Savvi-x/wro-Motaqadima/v-photos/WhatsApp Image 2026-09-22 at 7.46.37 PM (2).jpeg

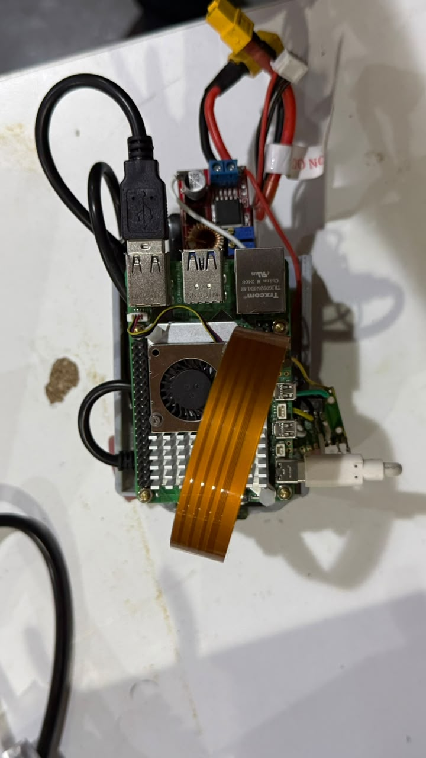
v-photos/WhatsApp Image 2026-09-22 at 7.46.37 PM (2).jpeg
