Savvi-x/wro-Motaqadima/v-photos/WhatsApp Image 2026-09-22 at 7.46.36 PM.jpeg

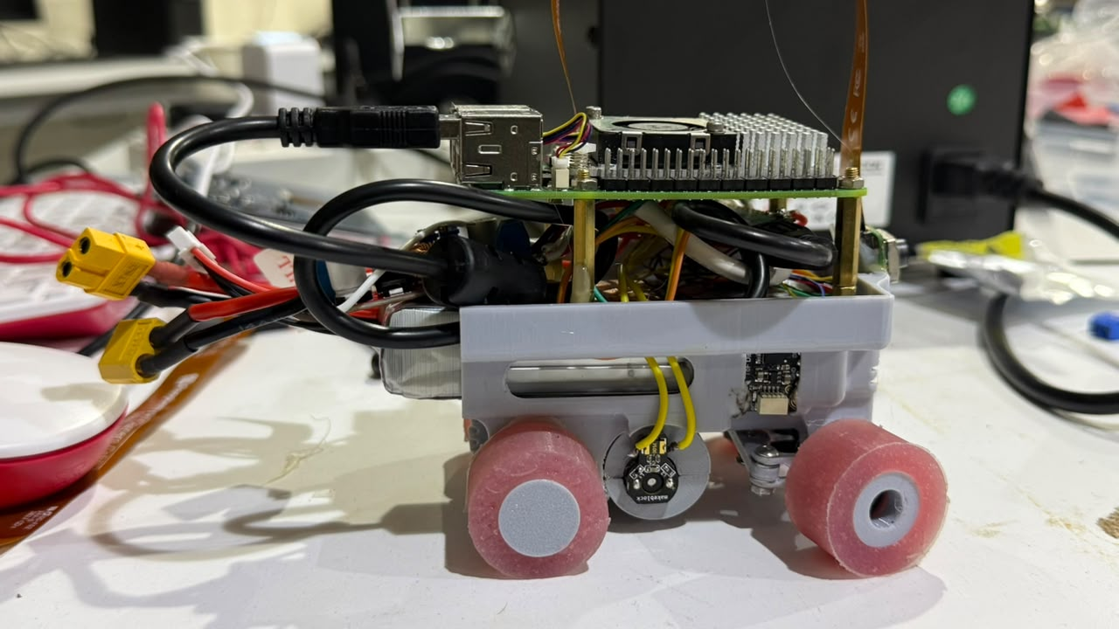
v-photos/WhatsApp Image 2026-09-22 at 7.46.36 PM.jpeg
