Savvi-x/wro-Motaqadima/models/3d_CAD_motion.gif

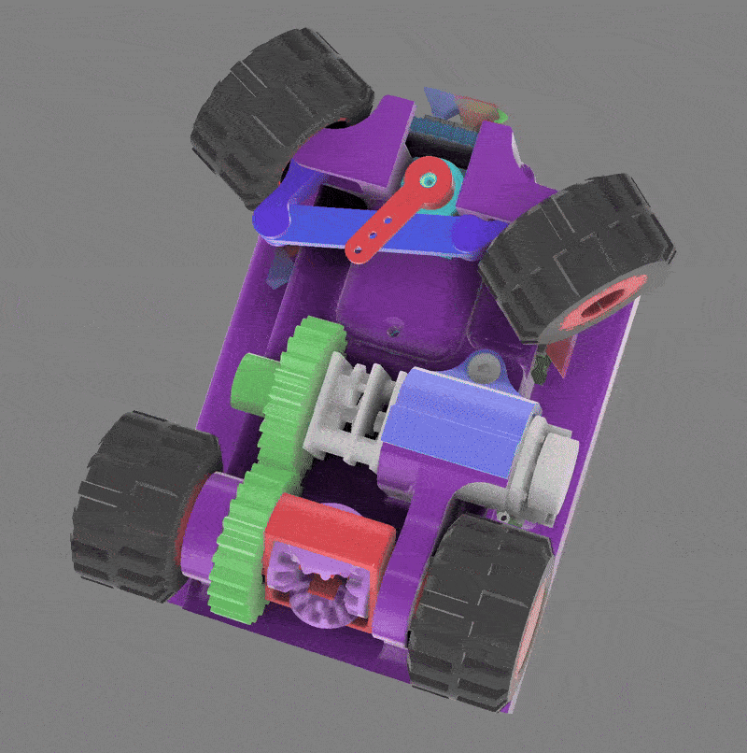
models/3d_CAD_motion.gif
