Savvi-x/wro-Motaqadima/models/CAD_design_4_gear_mini_differential_2.jpg

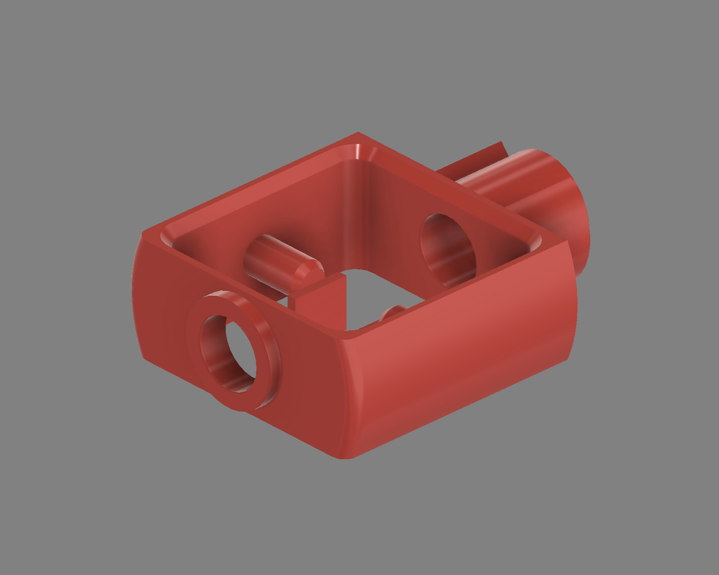
models/CAD_design_4_gear_mini_differential_2.jpg
