Savvi-x/wro-Motaqadima/models/CAD_design_bevel_12_gear_1.jpg

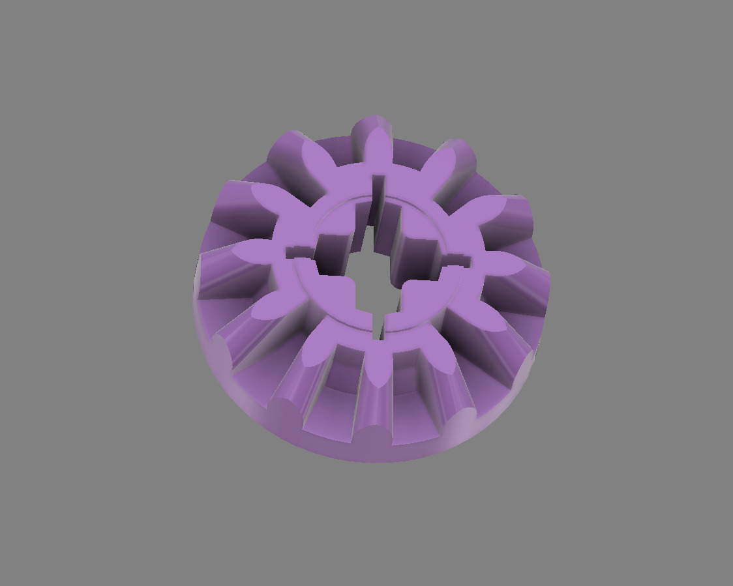
models/CAD_design_bevel_12_gear_1.jpg
