Savvi-x/wro-Motaqadima/models/CAD_design_front_rim_bearing_1.jpg

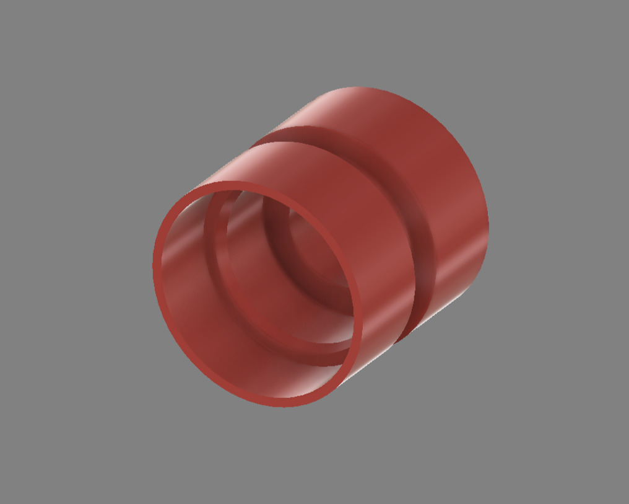
models/CAD_design_front_rim_bearing_1.jpg
