Savvi-x/wro-Motaqadima/models/CAD_design_front_rim_bearing_2.jpg

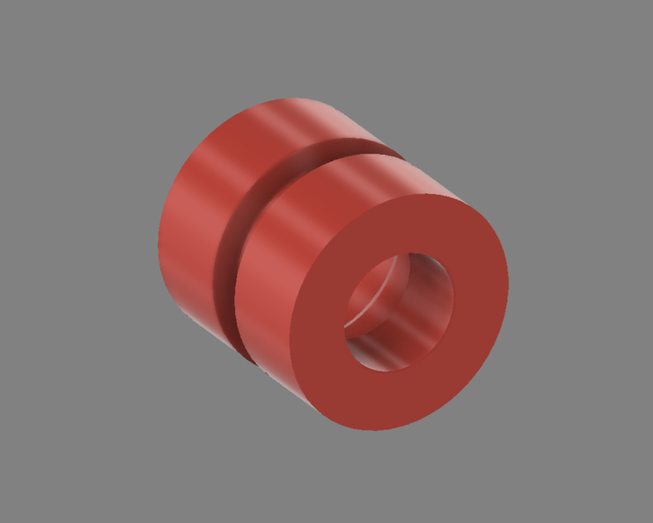
models/CAD_design_front_rim_bearing_2.jpg
