Savvi-x/wro-Motaqadima/models/CAD_design_spur_26_gear_1.jpg

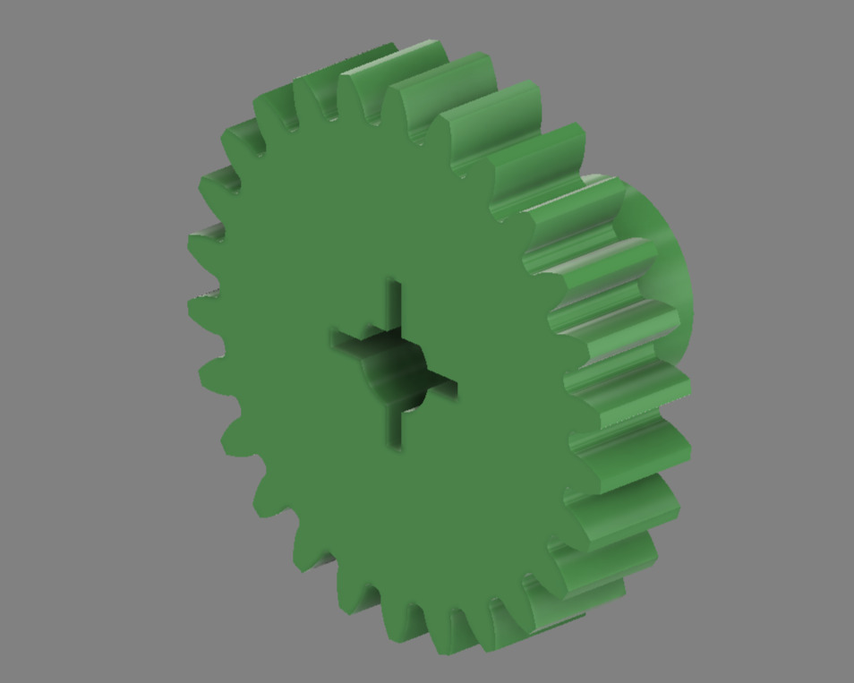
models/CAD_design_spur_26_gear_1.jpg
