Savvi-x/wro-Motaqadima/models/CAD_design_steering_arm_2.jpg

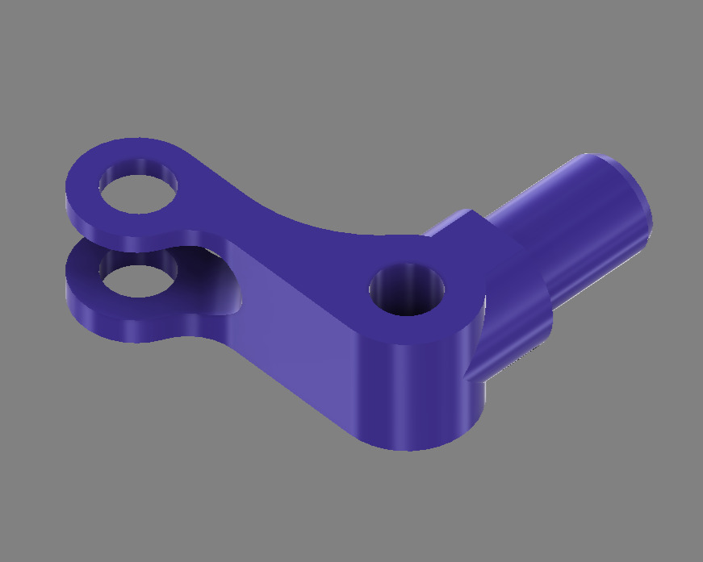
models/CAD_design_steering_arm_2.jpg
