Savvi-x/wro-Motaqadima/models/CAD_design_steering_linkage.jpg

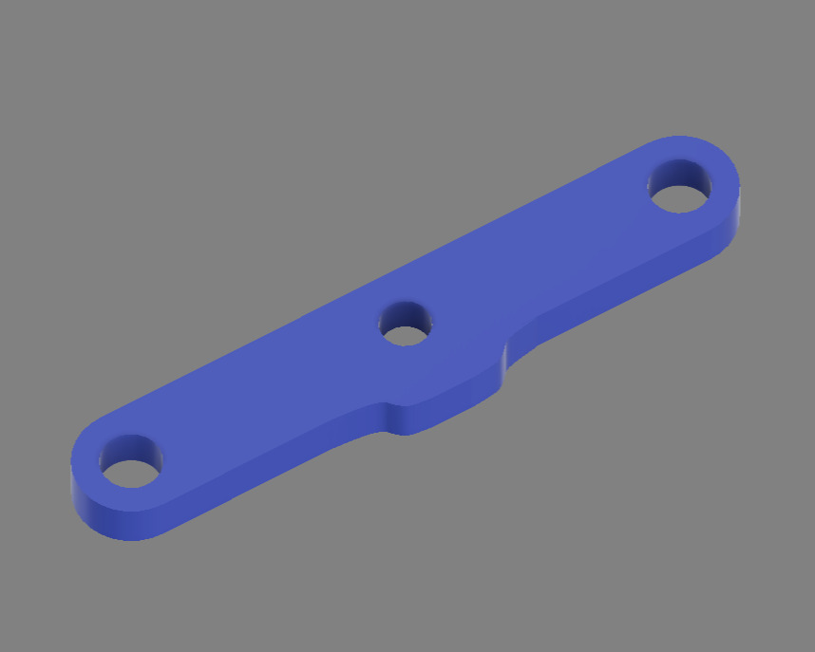
models/CAD_design_steering_linkage.jpg
