Savvi-x/wro-Motaqadima/models/CAD_fusion_isometric_view.jpg

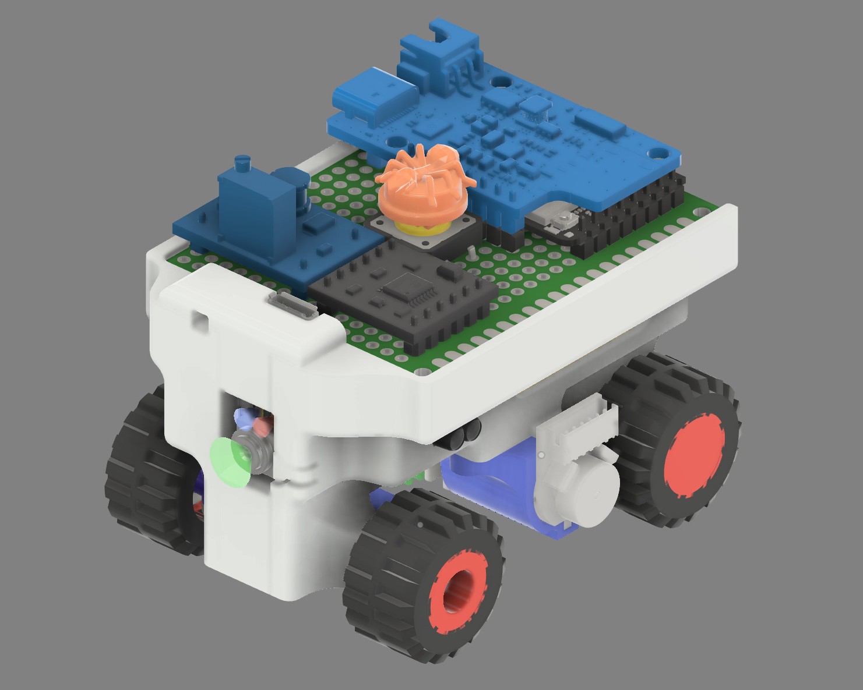
models/CAD_fusion_isometric_view.jpg
