Savvi-x/wro-Motaqadima/schemes/1.png

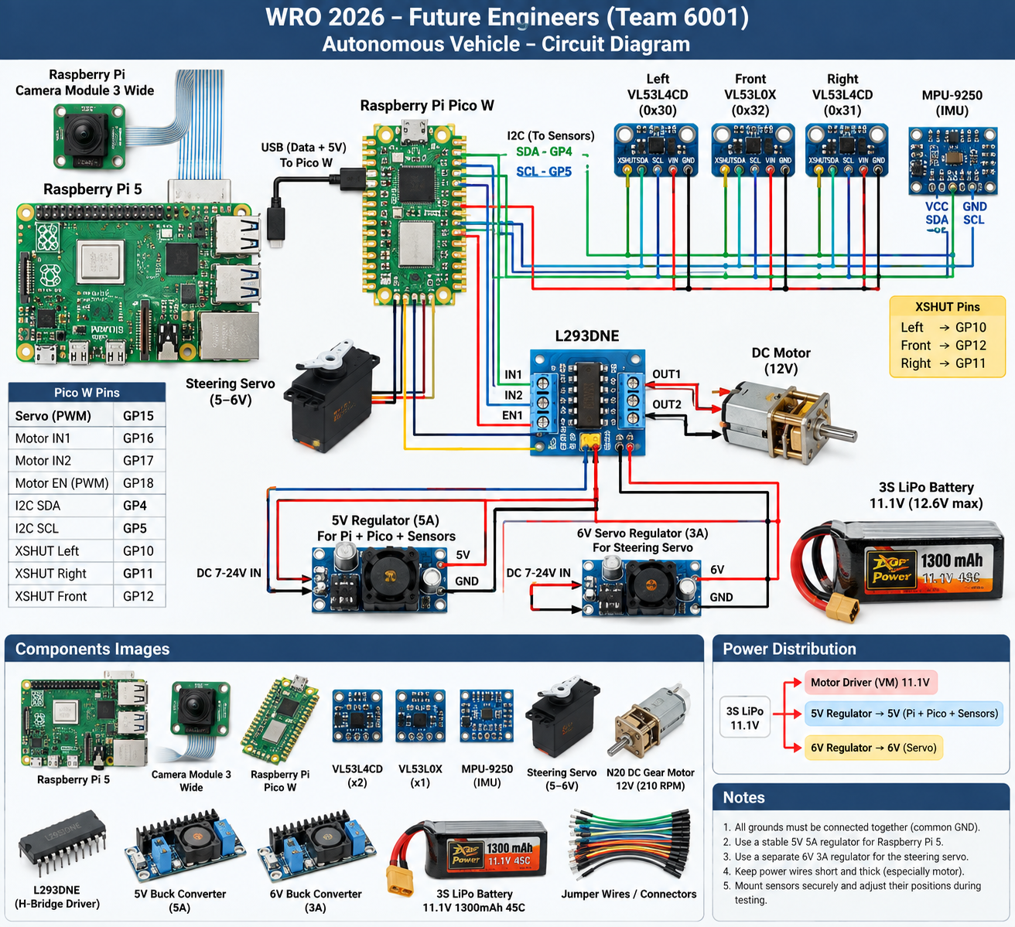
schemes/1.png
