Savvi-x/wro-Motaqadima/schemes/51fkXdb7u5L._AC_UF1000,1000_QL80_.jpg

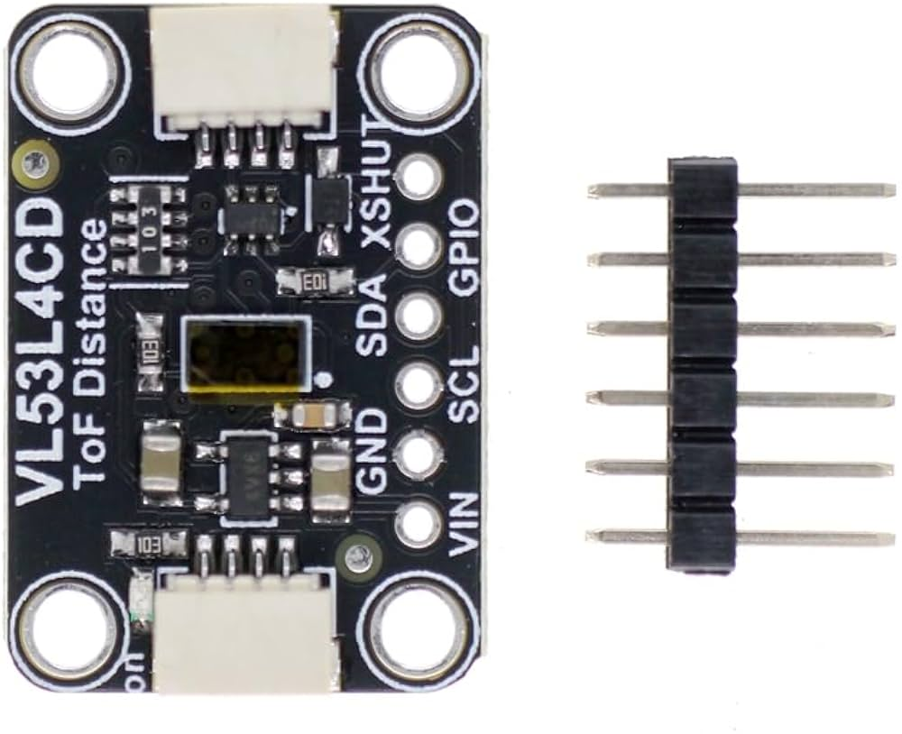
schemes/51fkXdb7u5L._AC_UF1000,1000_QL80_.jpg
