Savvi-x/wro-Motaqadima/schemes/sen-03-005-2.jpg

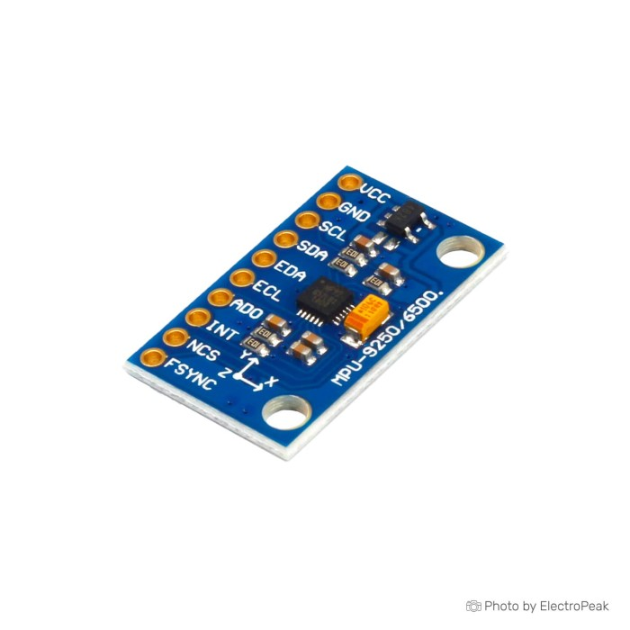
schemes/sen-03-005-2.jpg
