Savvi-x/wro-Motaqadima/src/example_all_detection.jpg

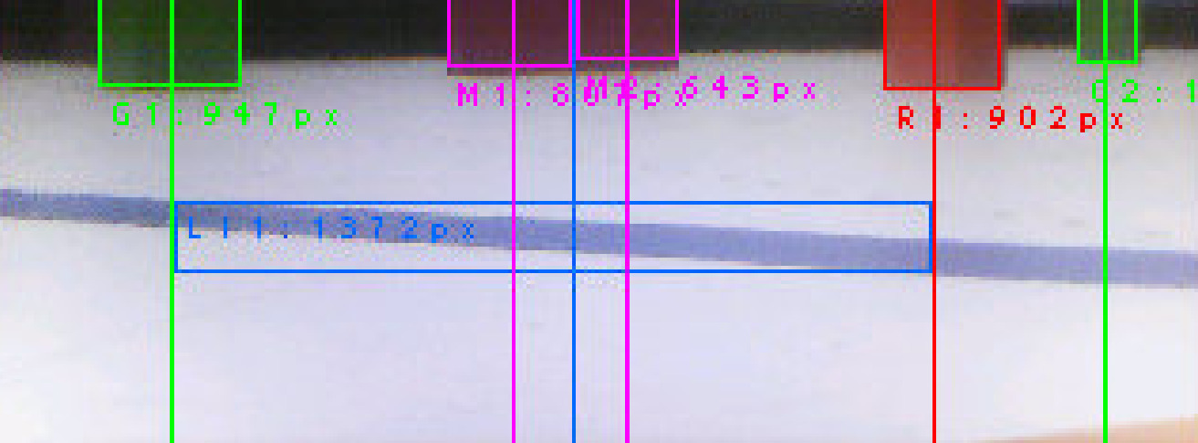
src/example_all_detection.jpg
