Savvi-x/wro-Motaqadima/src/obstacle_challenge_strategy_1.jpg

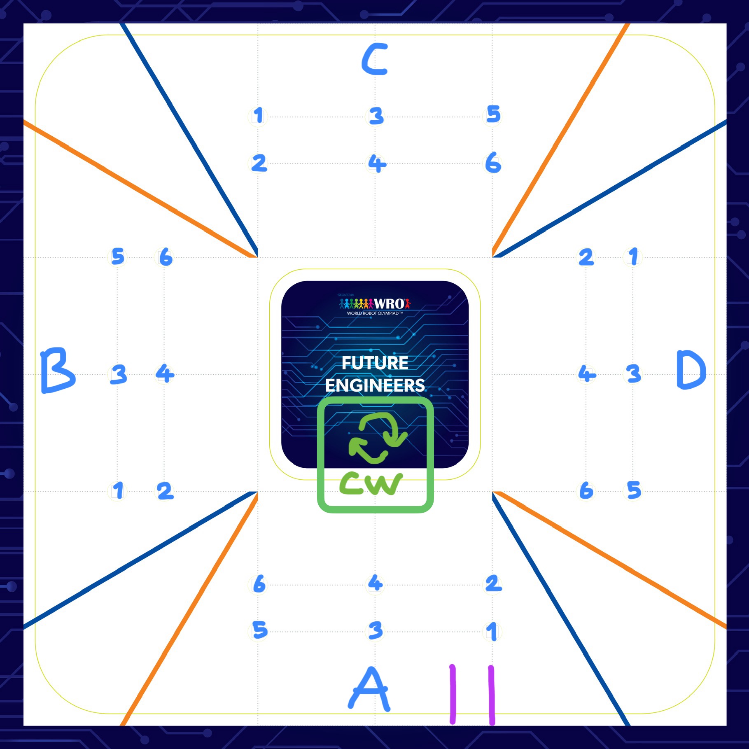
src/obstacle_challenge_strategy_1.jpg
