Savvi-x/wro-Motaqadima/src/parking_cube_strategy.jpg

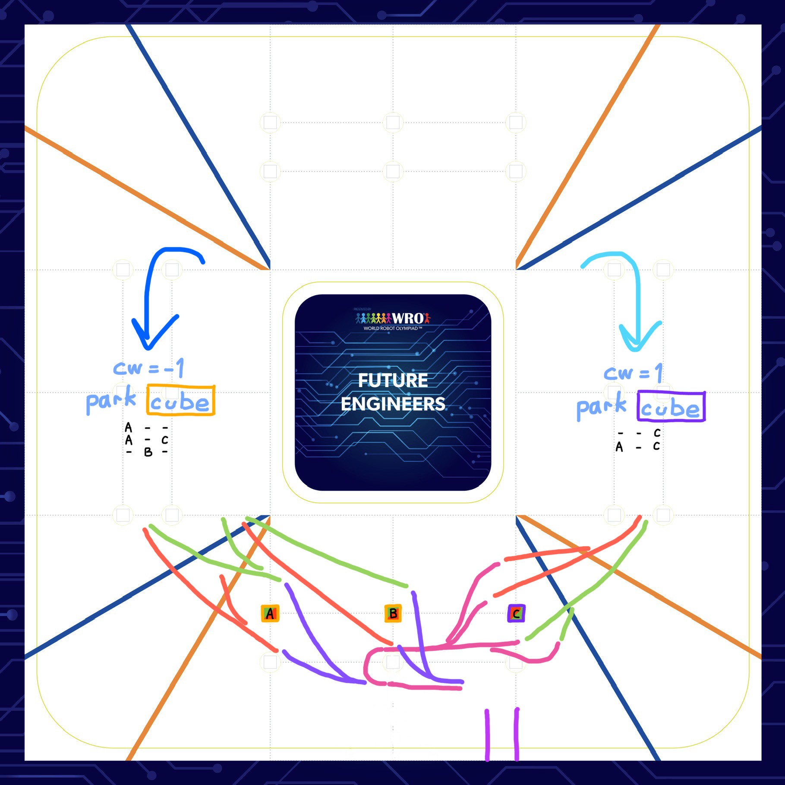
src/parking_cube_strategy.jpg
