Savvi-x/wro-Motaqadima/src/parking_cubeless_strategy.jpg

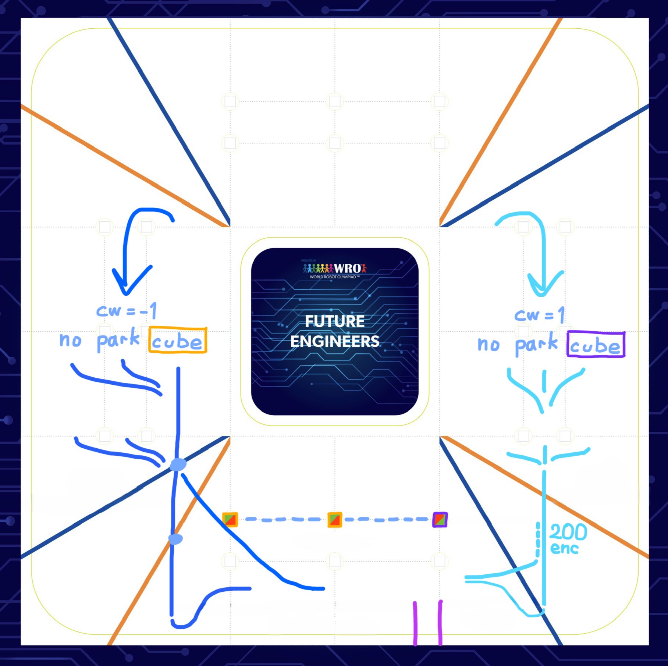
src/parking_cubeless_strategy.jpg
