Savvi-x/wro-Motaqadima/t-photos/WhatsApp Image 2026-09-22 at 7.53.52 PM (1).jpeg

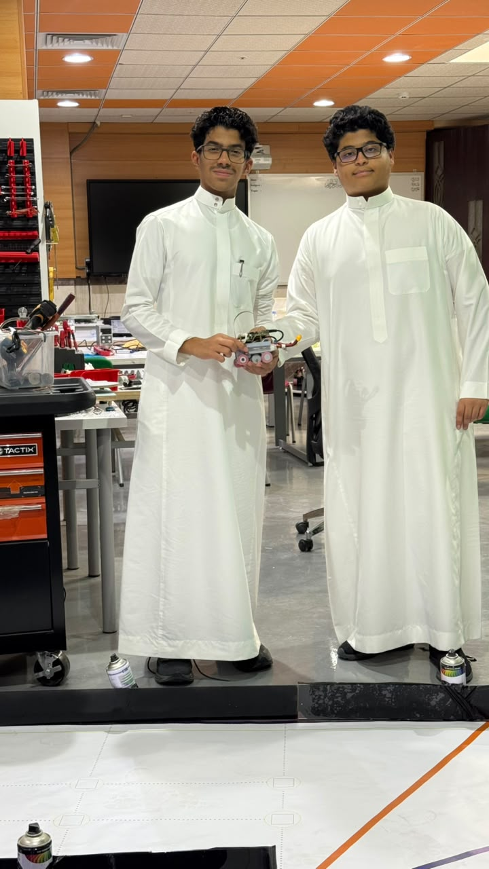
t-photos/WhatsApp Image 2026-09-22 at 7.53.52 PM (1).jpeg
